lykos98/nimbus/station-scripts/esp_c3/esp_c3_no_mqtt.ino

#include "soc/soc.h"
#include "soc/rtc_cntl_reg.h"
//#include "esp32s2/ulp.h"
//#include "soc/rtc_io_reg.h"
#include "driver/rtc_io.h"
#include "hal/gpio_types.h"

#include <rom/rtc.h>
#include "hal/brownout_hal.h"		// for adjusting brownout level

#define BME

#define SOLAR_PIN GPIO_NUM_1
#define BATTERY_PIN GPIO_NUM_0

#define AS5600_POWER_PIN GPIO_NUM_3
#define ANEMOMETER_PIN   GPIO_NUM_5
#define MAX_N_TRIES 10

#define RESET_PIN GPIO_NUM_4

#define SCL_PIN GPIO_NUM_9
#define SDA_PIN GPIO_NUM_8

#define ANEMOMETER_LEN 0.13
#define SLEEP_TIME 60 * 10
#define M_PI 3.14159265358979323846
#define API_URL "https://hehe.lykos.cc/api/stations/"


#include "esp32_utilities.h"
//#include "ulp_program.h"

HTTPClient http;



#ifdef BME
  #include <Adafruit_BME280.h>

  Adafruit_BME280 bmp; // I2C
#else
  #include <Adafruit_AHTX0.h>
  #include <Adafruit_BMP280.h>
  Adafruit_AHTX0  aht;
  Adafruit_BMP280 bmp(&Wire); // I2C
#endif
int count = 0;
uint32_t anemometer_rotations = 0;

void print_reset_reason(esp_reset_reason_t reason)
{
  switch (reason)
  {
    case ESP_RST_UNKNOWN:
      LOGF("ESP_RST_UNKNOWN");
      break;
    case ESP_RST_POWERON:
      LOGF("ESP_RST_POWERON");
      break;
    case ESP_RST_EXT:
      LOGF("ESP_RST_EXT");
      break;
    case ESP_RST_SW:
      LOGF("ESP_RST_SW");
      break;
    case ESP_RST_PANIC:
      LOGF("ESP_RST_PANIC");
      break;
    case ESP_RST_INT_WDT:
      LOGF("ESP_RST_INT_WDT");
      break;
    case ESP_RST_TASK_WDT:
      LOGF("ESP_RST_TASK_WDT");
      break;
    case ESP_RST_WDT:
      LOGF("ESP_RST_WDT");
      break;
    case ESP_RST_DEEPSLEEP:
      LOGF("ESP_RST_DEEPSLEEP");
      break;
    case ESP_RST_BROWNOUT:
      LOGF("ESP_RST_BROWNOUT");
      break;
    case ESP_RST_SDIO:
      LOGF("ESP_RST_SDIO");
      break;
    case ESP_RST_USB:
      LOGF("ESP_RST_USB");
      break;
    case ESP_RST_JTAG:
      LOGF("ESP_RST_JTAG");
      break;
    case ESP_RST_EFUSE:
      LOGF("ESP_RST_EFUSE");
      break;
    case ESP_RST_PWR_GLITCH:
      LOGF("ESP_RST_PWR_GLITCH");
      break;
    case ESP_RST_CPU_LOCKUP:
      LOGF("ESP_RST_CPU_LOCKUP");
      break;
    default:
      break;    
  }
}

int send_to_api(char* message)
{
  String url = String(API_URL) + String(STATION_ID) + "/data";

  http.begin(url);
  //LOGF("Sending to %s\n", url.c_str());
  http.addHeader("Content-Type", "application/json");
  int code = http.POST(message);
  http.end();
  return code;
}

void bmp_sleep() {
#ifdef BME
  bmp.setSampling(Adafruit_BME280::MODE_SLEEP);
#else
  bmp.setSampling(Adafruit_BMP280::MODE_SLEEP);
#endif
}

void setup() {
  char message[LOG_BUFFER_SIZE];

  /* disable brownout sensor */    
  brownout_hal_config_t cfg = {
    .threshold = 7,			// 3.00v
    .enabled = false,
    .reset_enabled = false,		// if you want to use ".det" as a software signal, you must disable all brown-out shutdowns
    .flash_power_down = false,
    .rf_power_down = false,
  };
  brownout_hal_config(&cfg);

  /* 
   * start up as5600 sensor
   * powered down for energy consumption 
   */

  pinMode(GPIO_NUM_3, OUTPUT);
  digitalWrite(GPIO_NUM_3, HIGH);


  /* 
   * Init serial and wait for initialization 
   * TODO: fine tune it to better have the
   * minimal number of seconds to sleep
   */
  Serial.begin(115200);
  delay(1000);
  

  LOGF("\n\n---------------------------------------------------");
  LOGF("RESET REASON");
  esp_reset_reason_t  reason = esp_reset_reason();
  print_reset_reason(reason);
  
  Wire.begin(SDA_PIN, SCL_PIN);

  /* 
   * check if initial config
   * SSID, password and possible configs need to be reset
   */
  connect_to_wifi();
    
  /* retrieve certificate and connect to the mqtt broker */

  /*
   * Initialize aht 
   */
 int tries = 0;
#ifdef BME 
  while(!bmp.begin(0x76))
  {
      delay(500);
      LOGF("Cannot initialize bmp");
      ++tries;
  }

  if(tries == MAX_N_TRIES)
  {
    snprintf( message, LOG_BUFFER_SIZE, 
              "{\"stationId\":\"%s\",\"error\":\"Cannot initialize BMP\",\"secret\":\"%s\"}", STATION_ID, SECRET);
    send_to_api(message);
    delay(500);
    esp_sleep_enable_timer_wakeup(SLEEP_TIME * 1000 * 1000);
    esp_deep_sleep_start();
  }
    float t = bmp.readTemperature();

  // Compute heat index in Celsius (isFahreheit = false)
  //float hic = dht.computeHeatIndex(t, h, false);

  float p = bmp.readPressure();

  float h = bmp.readHumidity();
#else
 
  while (aht.begin(&Wire) != true && tries < MAX_N_TRIES)
  {
    LOGF("AHT20 not connected or fail to load calibration coefficient"); 
    delay(5000);
    ++tries;
  }
 
  if(tries == MAX_N_TRIES)
  {
    snprintf( message, LOG_BUFFER_SIZE,
              "{\"stationId\":\"%s\",\"error\":\"Cannot initialize AHT\",\"secret\":\"%s\"}", STATION_ID, SECRET);
    send_to_api(message);
    delay(500);
    esp_sleep_enable_timer_wakeup(SLEEP_TIME * 1000 * 1000);
    esp_deep_sleep_start();
  }
  
  /* 
   * initialize BMP
   */

  tries = 0;
  //if(!bmp.begin(BMP280_ADDRESS_ALT, BMP280_CHIPID)){
  while(!bmp.begin() && tries < MAX_N_TRIES)
  {
      delay(500);
      LOGF("Cannot initialize bmp");
      ++tries;
  }

  if(tries == MAX_N_TRIES)
  {
    snprintf( message, LOG_BUFFER_SIZE, 
              "{\"stationId\":\"%s\",\"error\":\"Cannot initialize BMP\",\"secret\":\"%s\"}", STATION_ID, SECRET);
    send_to_api(message);
    delay(500);
    esp_sleep_enable_timer_wakeup(SLEEP_TIME * 1000 * 1000);
    esp_deep_sleep_start();
  }


  LOGF("Sensors initialized");

  /* reading sensor values */

  sensors_event_t aht_temp, aht_hum;
  aht.getEvent(&aht_hum, &aht_temp);
  float t = (bmp.readTemperature() + aht_temp.temperature ) /2.;
  float p = bmp.readPressure();
  float h = aht_hum.relative_humidity;

  LOGF("Read from bmp & aht");
#endif 

  /* reading battery and solar voltages */

  float battery_voltage = read_avg_v(BATTERY_PIN);
  float solar_voltage = read_avg_v(SOLAR_PIN);
  LOGF("Read battery V and solar V");

  LOGF("Sensors value read");

  /* composing mesage and sending */
  snprintf(message, LOG_BUFFER_SIZE,
            "{\"stationId\":\"%s\","
            "\"airHumidity\":%.2f,"
            "\"airTemperature\":%.2f,"
            "\"airPressure\":%.2f,"
            "\"solarV\":%.2f,"
            "\"batteryV\":%.2f,"
            "\"RSSI\":%ld, \"secret\":\"%s\"}",
          STATION_ID,h,t,p,solar_voltage, battery_voltage, WiFi.RSSI(), SECRET); 
  LOGF("Message built");
  //LOGF(message);
  int code = send_to_api(message);
  LOGF("Message send with code: %d", code);
  delay(100);
  
  /* disconnect from wifi and start the ULP */
  WiFi.disconnect();

  /* Go to deep sleep */
  //esp_sleep_enable_ulp_wakeup();
  esp_sleep_enable_timer_wakeup(SLEEP_TIME *1000 * 1000);

  /* turn off a5600 and bmp */
  digitalWrite(GPIO_NUM_3, LOW);
  bmp_sleep();
  esp_deep_sleep_start();
 
}

void loop() {}
